dcpedit/tklish/pcb-040/Matrix.kicad_sch

## KiCad design pcb-040/Matrix.kicad_sch (2025-01-22)

Schematic: Matrix.kicad_sch

Parts:
D10, D12, D13, D14, D15, D16, D18, D19, D20, D21, D22, D24, D25, D26, D27, D28, D30, D31, D32, D33, D34, D36, D37, D38, D39, D40, D42, D43, D44, D45, D58, D60, D61, D62, D63, D64, D66, D67, D68, D69, D70, D72, D73, D74, D75, D76, D78, D79, D80, D81, D82, D84, D85, D86, D87, D88, D90, D91, D92, D93, D94, D97, D98, D99, D100, D102, D103, D104, D105: LCSC C81598
MX10, MX12, MX14, MX15, MX15.125, MX16, MX18, MX19, MX20, MX21, MX22, MX24, MX25, MX26, MX27, MX27.15, MX28, MX30, MX31, MX32, MX33, MX34, MX36, MX37, MX38, MX39, MX40, MX42, MX43, MX44, MX45, MX45.2, MX58, MX60, MX61, MX62, MX63, MX63.2, MX64, MX66, MX67, MX68, MX69, MX70, MX72, MX73, MX74, MX75, MX76, MX78, MX79, MX80, MX81, MX81.15, MX82, MX84, MX85, MX86, MX87, MX88, MX90, MX91, MX92, MX93, MX93.125, MX97, MX98, MX99, MX100, MX102, MX103, MX104, MX105: MX-NoLED; MXOnly-1U-NoLED
MX13, MX94: MX-LED
R2, R3: 470
SWR1, SWR2, SWR3: RotaryEncoder_Switch

Connections:
COL0: MX10.1 (COL), MX12.1 (COL), MX13.1 (COL), MX14.1 (COL), MX15.1 (COL), MX15.125.1 (COL), MX16.1 (COL), MX18.1 (COL), MX19.1 (COL), MX20.1 (COL), MX21.1 (COL)
COL1: MX22.1 (COL), MX24.1 (COL), MX25.1 (COL), MX26.1 (COL), MX27.1 (COL), MX27.15.1 (COL), MX28.1 (COL), MX30.1 (COL), MX31.1 (COL), MX32.1 (COL), MX33.1 (COL)
COL2: MX34.1 (COL), MX36.1 (COL), MX37.1 (COL), MX38.1 (COL), MX39.1 (COL), MX40.1 (COL), MX42.1 (COL), MX43.1 (COL), MX44.1 (COL), MX45.1 (COL), MX45.2.1 (COL)
COL4: MX58.1 (COL), MX60.1 (COL), MX61.1 (COL), MX62.1 (COL), MX63.1 (COL), MX63.2.1 (COL), MX64.1 (COL), MX66.1 (COL), MX67.1 (COL), MX68.1 (COL), MX69.1 (COL)
COL5: MX70.1 (COL), MX72.1 (COL), MX73.1 (COL), MX74.1 (COL), MX75.1 (COL), MX76.1 (COL), MX78.1 (COL), MX79.1 (COL), MX80.1 (COL), MX81.1 (COL), MX81.15.1 (COL)
COL6: MX82.1 (COL), MX84.1 (COL), MX85.1 (COL), MX86.1 (COL), MX87.1 (COL), MX88.1 (COL), MX90.1 (COL), MX91.1 (COL), MX92.1 (COL), MX93.1 (COL), MX93.125.1 (COL), SWR1.S1
COL7: MX94.1 (COL), MX97.1 (COL), MX98.1 (COL), MX99.1 (COL), MX100.1 (COL), MX102.1 (COL), MX103.1 (COL), MX104.1 (COL), MX105.1 (COL), SWR2.S1, SWR3.S1
GND: R2.2, R3.2, SWR1.C, SWR2.C, SWR3.C
LED_CAPS: MX13.3 (LED)
LED_SLCK: MX94.3 (LED)
unnamed: D10.2 (A), MX10.2 (ROW)
unnamed: D12.2 (A), MX12.2 (ROW)
unnamed: D13.2 (A), MX13.2 (ROW)
unnamed: D14.2 (A), MX14.2 (ROW)
unnamed: D15.2 (A), MX15.2 (ROW), MX15.125.2 (ROW)
unnamed: D16.2 (A), MX16.2 (ROW)
unnamed: D18.2 (A), MX18.2 (ROW)
unnamed: D19.2 (A), MX19.2 (ROW)
unnamed: D20.2 (A), MX20.2 (ROW)
unnamed: D21.2 (A), MX21.2 (ROW)
unnamed: D22.2 (A), MX22.2 (ROW)
unnamed: D24.2 (A), MX24.2 (ROW)
unnamed: D25.2 (A), MX25.2 (ROW)
unnamed: D26.2 (A), MX26.2 (ROW)
unnamed: D27.2 (A), MX27.2 (ROW), MX27.15.2 (ROW)
unnamed: D28.2 (A), MX28.2 (ROW)
unnamed: D30.2 (A), MX30.2 (ROW)
unnamed: D31.2 (A), MX31.2 (ROW)
unnamed: D32.2 (A), MX32.2 (ROW)
unnamed: D33.2 (A), MX33.2 (ROW)
unnamed: D34.2 (A), MX34.2 (ROW)
unnamed: D36.2 (A), MX36.2 (ROW)
unnamed: D37.2 (A), MX37.2 (ROW)
unnamed: D38.2 (A), MX38.2 (ROW)
unnamed: D39.2 (A), MX39.2 (ROW)
unnamed: D40.2 (A), MX40.2 (ROW)
unnamed: D42.2 (A), MX42.2 (ROW)
unnamed: D43.2 (A), MX43.2 (ROW)
unnamed: D44.2 (A), MX44.2 (ROW)
unnamed: D45.2 (A), MX45.2 (ROW), MX45.2.2 (ROW)
unnamed: D58.2 (A), MX58.2 (ROW)
unnamed: D60.2 (A), MX60.2 (ROW)
unnamed: D61.2 (A), MX61.2 (ROW)
unnamed: D62.2 (A), MX62.2 (ROW)
unnamed: D63.2 (A), MX63.2 (ROW), MX63.2.2 (ROW)
unnamed: D64.2 (A), MX64.2 (ROW)
unnamed: D66.2 (A), MX66.2 (ROW)
unnamed: D67.2 (A), MX67.2 (ROW)
unnamed: D68.2 (A), MX68.2 (ROW)
unnamed: D69.2 (A), MX69.2 (ROW)
unnamed: D70.2 (A), MX70.2 (ROW)
unnamed: D72.2 (A), MX72.2 (ROW)
unnamed: D73.2 (A), MX73.2 (ROW)
unnamed: D74.2 (A), MX74.2 (ROW)
unnamed: D75.2 (A), MX75.2 (ROW)
unnamed: D76.2 (A), MX76.2 (ROW)
unnamed: D78.2 (A), MX78.2 (ROW)
unnamed: D79.2 (A), MX79.2 (ROW)
unnamed: D80.2 (A), MX80.2 (ROW)
unnamed: D81.2 (A), MX81.2 (ROW), MX81.15.2 (ROW)
unnamed: D82.2 (A), MX82.2 (ROW)
unnamed: D84.2 (A), MX84.2 (ROW)
unnamed: D85.2 (A), MX85.2 (ROW)
unnamed: D86.2 (A), MX86.2 (ROW)
unnamed: D87.2 (A), MX87.2 (ROW)
unnamed: D88.2 (A), MX88.2 (ROW), SWR1.S2
unnamed: D90.2 (A), MX90.2 (ROW)
unnamed: D91.2 (A), MX91.2 (ROW)
unnamed: D92.2 (A), MX92.2 (ROW)
unnamed: D93.2 (A), MX93.2 (ROW), MX93.125.2 (ROW)
unnamed: D94.2 (A), MX94.2 (ROW), SWR2.S2
unnamed: D97.2 (A), MX97.2 (ROW)
unnamed: D98.2 (A), MX98.2 (ROW)
unnamed: D99.2 (A), MX99.2 (ROW)
unnamed: D100.2 (A), MX100.2 (ROW), SWR3.S2
unnamed: D102.2 (A), MX102.2 (ROW)
unnamed: D103.2 (A), MX103.2 (ROW)
unnamed: D104.2 (A), MX104.2 (ROW)
unnamed: D105.2 (A), MX105.2 (ROW)
unnamed: MX13.4 (LEDGND), R2.1
unnamed: MX94.4 (LEDGND), R3.1
RE1: SWR1.A, SWR2.A
RE2: SWR1.B, SWR3.A
RE3: SWR2.B, SWR3.B
ROW0: D10.1 (K), D22.1 (K), D34.1 (K), D58.1 (K), D70.1 (K), D82.1 (K), D94.1 (K)
ROW2: D12.1 (K), D24.1 (K), D36.1 (K), D60.1 (K), D72.1 (K), D84.1 (K)
ROW3: D13.1 (K), D25.1 (K), D37.1 (K), D61.1 (K), D73.1 (K), D85.1 (K), D97.1 (K)
ROW4: D14.1 (K), D26.1 (K), D38.1 (K), D62.1 (K), D74.1 (K), D86.1 (K), D98.1 (K)
ROW5: D15.1 (K), D27.1 (K), D39.1 (K), D63.1 (K), D75.1 (K), D87.1 (K), D99.1 (K)
ROW6: D16.1 (K), D28.1 (K), D40.1 (K), D64.1 (K), D76.1 (K), D88.1 (K), D100.1 (K)
ROW8: D18.1 (K), D30.1 (K), D42.1 (K), D66.1 (K), D78.1 (K), D90.1 (K), D102.1 (K)
ROW9: D19.1 (K), D31.1 (K), D43.1 (K), D67.1 (K), D79.1 (K), D91.1 (K), D103.1 (K)
ROW10: D20.1 (K), D32.1 (K), D44.1 (K), D68.1 (K), D80.1 (K), D92.1 (K), D104.1 (K)
ROW11: D21.1 (K), D33.1 (K), D45.1 (K), D69.1 (K), D81.1 (K), D93.1 (K), D105.1 (K)
