dcpedit/tklish/pcb-40/pcb-40.kicad_sch

## KiCad design pcb-40/pcb-40.kicad_sch (2024-10-09)

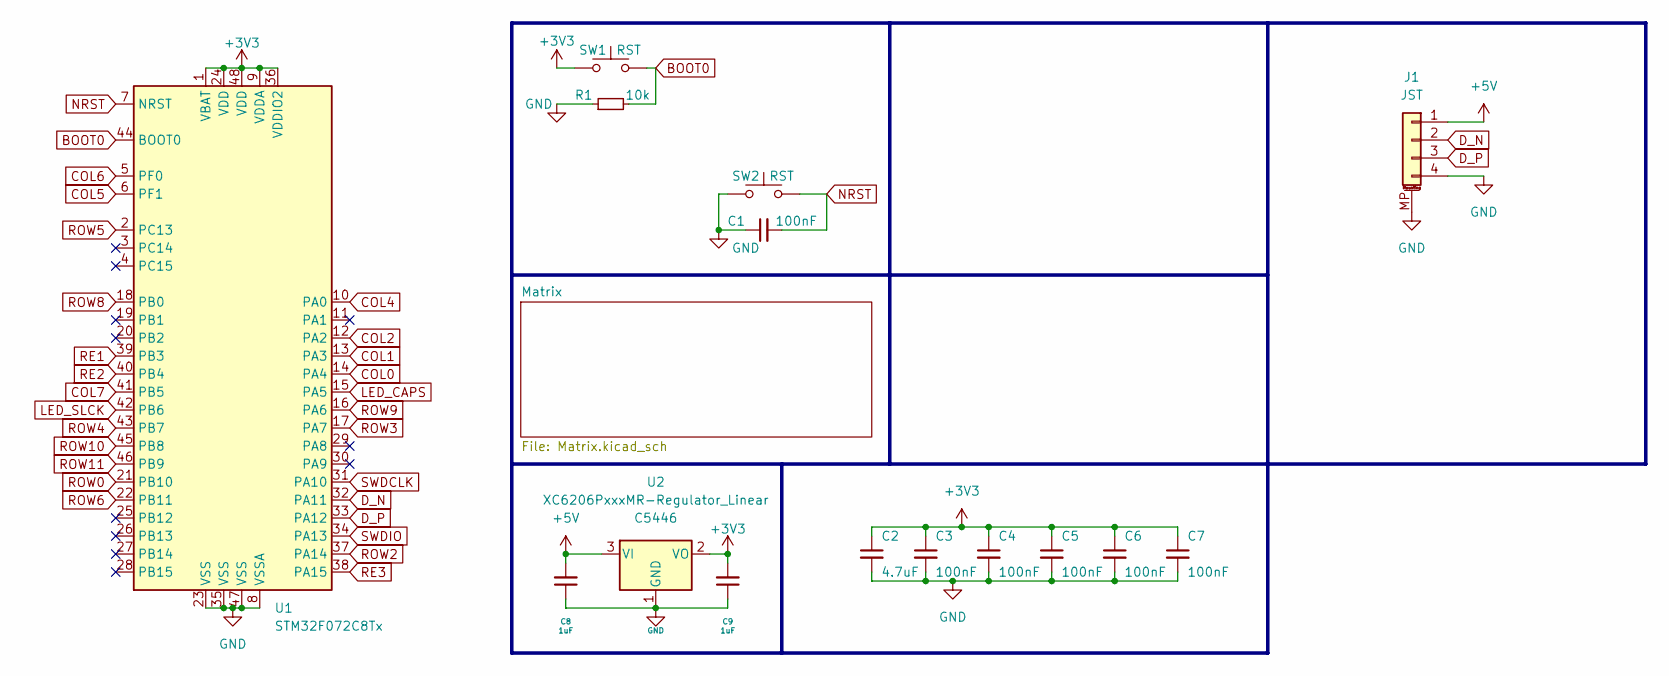
[picture p2: schematic pcb-40.kicad_sch]

Parts:
C1, C3, C4, C5, C6, C7: 100nF; C_0402_1005Metric; LCSC C307331
C2: 4.7uF; C_0402_1005Metric; LCSC C23733
C8, C9: 1uF; C_0402_1005Metric; LCSC C52923
J1: JST; MOLEX_781710004_MountingReliefs; LCSC C588524
R1: 10k; R_0402_1005Metric; LCSC C25744
SW1, SW2: RST; SW_SPST_SKQG_WithoutStem; LCSC C318884
U1: STM32F072C8Tx; LQFP-48_7x7mm_P0.5mm; LCSC C80488
U2: XC6206PxxxMR-Regulator_Linear; SOT-23; LCSC C5446

Connections:
+3V3: C2.1, C3.1, C4.1, C5.1, C6.1, C7.1, C9.2, SW1.1, U1.1 (VBAT), U1.9 (VDDA), U1.24 (VDD), U1.36 (VDDIO2), U1.48 (VDD), U2.2 (VO)
+5V: C8.2, J1.1, U2.3 (VI)
BOOT0: R1.2, SW1.2, U1.44 (BOOT0)
COL0: U1.14 (PA4)
COL1: U1.13 (PA3)
COL2: U1.12 (PA2)
COL4: U1.10 (PA0)
COL5: U1.6 (PF1)
COL6: U1.5 (PF0)
COL7: U1.41 (PB5)
D_N: J1.2, U1.32 (PA11)
D_P: J1.3, U1.33 (PA12)
GND: C1.1, C2.2, C3.2, C4.2, C5.2, C6.2, C7.2, C8.1, C9.1, J1.4, J1.MP (MountPin), R1.1, SW2.1, U1.8 (VSSA), U1.23 (VSS), U1.35 (VSS), U1.47 (VSS), U2.1 (GND)
LED_CAPS: U1.15 (PA5)
LED_SLCK: U1.42 (PB6)
NRST: C1.2, SW2.2, U1.7 (NRST)
RE1: U1.39 (PB3)
RE2: U1.40 (PB4)
RE3: U1.38 (PA15)
ROW0: U1.21 (PB10)
ROW2: U1.37 (PA14)
ROW3: U1.17 (PA7)
ROW4: U1.43 (PB7)
ROW5: U1.2 (PC13)
ROW6: U1.22 (PB11)
ROW8: U1.18 (PB0)
ROW9: U1.16 (PA6)
ROW10: U1.45 (PB8)
ROW11: U1.46 (PB9)
SWDCLK: U1.31 (PA10)
SWDIO: U1.34 (PA13)
